DyadicGit/automatic-ventilation-arduino/asserts/gas sensors test results.txt

2018-24-08 07:24.150:	Started Serial in HVAC

2018-24-08 07:24.210:	CO2: 90
2018-24-08 07:24.210:	CH4: 240
2018-24-08 07:24.210:	temp: 23.3C

2018-24-08 07:24.310:	CO2: 90
2018-24-08 07:24.310:	CH4: 240
2018-24-08 07:24.310:	temp: 23.3C

2018-24-08 07:24.410:	CO2: 90
2018-24-08 07:24.410:	CH4: 240
2018-24-08 07:24.410:	temp: 23.3C

2018-24-08 07:24.510:	
2018-24-08 07:24.510:	CO2: 100
2018-24-08 07:24.510:	CH4: 240

2018-24-08 07:24.510:	temp: 23.3C
2018-25-08 07:25.010:	CO2: 100
2018-25-08 07:25.010:	CH4: 240

2018-25-08 07:25.010:	temp: 23.3C
2018-25-08 07:25.110:	
2018-25-08 07:25.110:	CO2: 90

2018-25-08 07:25.110:	CH4: 240
2018-25-08 07:25.110:	temp: 23.4C
2018-25-08 07:25.210:	CO2: 90

2018-25-08 07:25.210:	CH4: 240
2018-25-08 07:25.210:	temp: 23.4C
2018-25-08 07:25.310:	CO2: 90

2018-25-08 07:25.310:	CH4: 230
2018-25-08 07:25.310:	temp: 23.4C
2018-25-08 07:25.410:	CO2: 90

2018-25-08 07:25.410:	CH4: 230
2018-25-08 07:25.410:	temp: 23.4C
2018-25-08 07:25.510:	CO2: 90

2018-25-08 07:25.510:	CH4: 230
2018-25-08 07:25.510:	temp: 23.4C
2018-26-08 07:26.010:	

2018-26-08 07:26.010:	CO2: 100
2018-26-08 07:26.010:	CH4: 230
2018-26-08 07:26.010:	temp: 23.5C

2018-26-08 07:26.110:	CO2: 90
2018-26-08 07:26.110:	CH4: 230
2018-26-08 07:26.110:	temp: 23.4C

2018-26-08 07:26.210:	CO2: 100
2018-26-08 07:26.210:	CH4: 230
2018-26-08 07:26.210:	temp: 23.4C

2018-26-08 07:26.310:	CO2: 100
2018-26-08 07:26.310:	CH4: 230
2018-26-08 07:26.310:	temp: 23.5C

2018-26-08 07:26.410:	CO2: 100
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

2018-39-09 01:39.510:	CO2: 180
2018-39-09 01:39.510:	CH4: 330
2018-39-09 01:39.510:	temp: 23.9C

2018-40-09 01:40.010:	CO2: 180
2018-40-09 01:40.010:	CH4: 330
2018-40-09 01:40.010:	temp: 23.9C

2018-40-09 01:40.110:	CO2: 180
2018-40-09 01:40.110:	CH4: 330
2018-40-09 01:40.110:	temp: 23.9C
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
